evangehler/SwampThing/sims/spice/SWAMP THING V0/Swamp thing V0.asc

ATTACK_POT: res; 10
BLEND_POT_LOW: res; 20k
BLEND_POT_UPPER: res; 80k
Buck: voltage; 10V
C1: cap; 100nF
C2: cap; 100nF
C3: cap; 2.2µF
C4: cap; 100nF
C5: cap; 1nF
C6: cap; 100nF
C7: cap; 1nF
C8: cap; 1nF
C9: cap; 1nF
C10: cap; 1nF
C11: cap; 100nF
D1: diode; 1N4148
D2: diode; 1N4148
D3: diode; 1N4148
D4: diode; 1N4148
D5: diode; 1N4148
D6: diode; 1N4148
D7: diode; 1N4148
D8: diode; 1N4148
D9: diode; 1N4148
D10: diode; 1N4148
D11: diode; 1N4148
D12: diode; 1N4148
D13: LED; QTLP690C
D14: LED; QTLP690C
E1: e; .4
EG_LIMIT: res; 13k
FILTER_CTF_POT_H: res; 90k
FILTER_CTF_POT_L: res; 1k
FILTER_EG_AMT_POT_H: res; 30k
FILTER_EG_AMT_POT_L: res; 70k
J2: njf; J112
Pi_Pico: current; 150mA
POT_SUB_VOLUME: res; 100
PWM_LIMIT_H: res; 4.7k
PWM_LIMIT_L: res; 27k
PWM_POT_LOWER: res; 10k
PWM_POT_UPPER: res; 90k
Q1: npn; 2N3904
Q2: npn; 2N3904
Q3: npn; 2N3904
R1: res; 500
R2: res; 1Meg
R3: res; 620
R4: res; 390k
R5: res; 1k
R6: res; 1Meg
R7: res; 100k
R8: res; 10k
R9: res; 1Meg
R11: res; 500
R12: res; 500
R13: res; 100k
R14: res; 3k
R15: res; 1k
R17: res; 220k
R18: res; 390k
R19: res; 1Meg
R20: res; 220k
R21: res; 220k
R22: res; 390k
R23: res; 1Meg
R24: res; 100k
R25: res; 1k
R26: res; 1.6Meg
R27: res; 1Meg
R28: res; 560k
R32: res; 2k
R33: res; 33k
R34: res; 33k
R35: res; 33k
R36: res; 33k
R37: res; 33k
R38: res; 33k
R39: res; 33k
R42: res; 100k
R43: res; 47k
R44: res; 14k
R50: res; 100k
R51: res; 68k
R53: res; 50k
R54: res; 50k
R55: res; 100k
R56: res; 1k
R57: res; 5k
R60: res; 1Meg
R_dead: res; 39k
R_dead_match: res; 39k
REL_POT: res; 180k
RESO_TRIMMER: res; 20k
U1: opamp2; TL072
U2: opamp2; TL072
U3: opamp2; TL072
U4: opamp2; TL072
U5: opamp2; TL072
U6: opamp2; TL072
U7: opamp2; TL072
U8: opamp2; TL072
U9: opamp2; TL072
U10: opamp2; TL072
U11: opamp2; TL072
U12: opamp2; TL072
U13: opamp2; TL072
U14: opamp2; TL072
U15: opamp2; TL072
U16: opamp2; TL072
U17: opamp2; TL072
U18: opamp2; TL072
U19: opamp2; TL072
V_drop: voltage; 30V
V_GATE: voltage; PULSE(0 3.3V 600ms 1us 1us 250ms 2s)
V_SAW: voltage; PULSE(0 10v 0 6.249ms .0010ms 0 6.25ms)
V_SUB: voltage; PULSE(0 10v 0 10ns 10ns 12.5ms 25ms)
VCA_BIAS_LIMIT_H: res; 47k
VCA_BIAS_LIMIT_L1: res; 8.2k
VCA_BIAS_LIMIT_L2: res; 1.8k
VCA_BIAS_TRIMMER_H: res; 15k
VCA_BIAS_TRIMMER_L: res; 35k
VCA_EG_LIMIT_H: res; 50k
VCA_EG_TRIMMER_H: res; 5k
VCA_EG_TRIMMER_L: res; 45k
VCC_Regulator: voltage; 3V
VEE_Regulator: voltage; 3V
VOLUME_POT: res; 50k
wallwart: voltage; 15V
Named nets: VCC, SAW, PULSE, 0, EG_TO_VCA, SUB, VEE, MIXER_+_SUB, VCA_OUT, EG_TO_VCF, VCF_OUT, OUTPUT, GATE_MSG, EG_TO_LED, JFET_BIAS, MIXER_OUT, VCF_out, RECORD, Vee
.tran 0 2.5s 500ms uic
.inc "[PATH_TO_THIS_FOLDER]\\TL072.cir"
.wave [PATH_TO_THIS_FOLDER]\\EXPORT\\simulation_output.wav" 16 44.1k V(RECORD)
POWER
OSC
BLEND
SPICE DIRECTIVES
VCA
This doesnt work because the tl072 spice model 
draws much much powerthan is listed on its data sheet
EG
VCF
Swamp Thing Monosynth V_0.0 - 12/13/2025
Evan Gehler
Julian La Rosa
Jack Payne
UF AES
OUTPUT STAGE
REPLACE ABOVE WITH FULL PATHWAY TO THIS FOLDER
NOTES
LED
50k trimmer
50k trimmer
100k B Pot
1Meg A pot
100k B pot
250kA pot
250kA pot
100k or 250k A pot
Pot
Trimmer
This is done to get some kind of BW limiting
on the sub. for simulation purposes only
Monitor output
Audio file will clip above +/-1V
consider 0-16k range
100k B pot
100k B pot
100k B pot
100k A pot
100k A pot
